MERL-Rose-Hulman/LilyBotCommon/3D Print Parts/NOLONGERUSE/motor_mount/solidworks/Motor Mount.SLDPRT

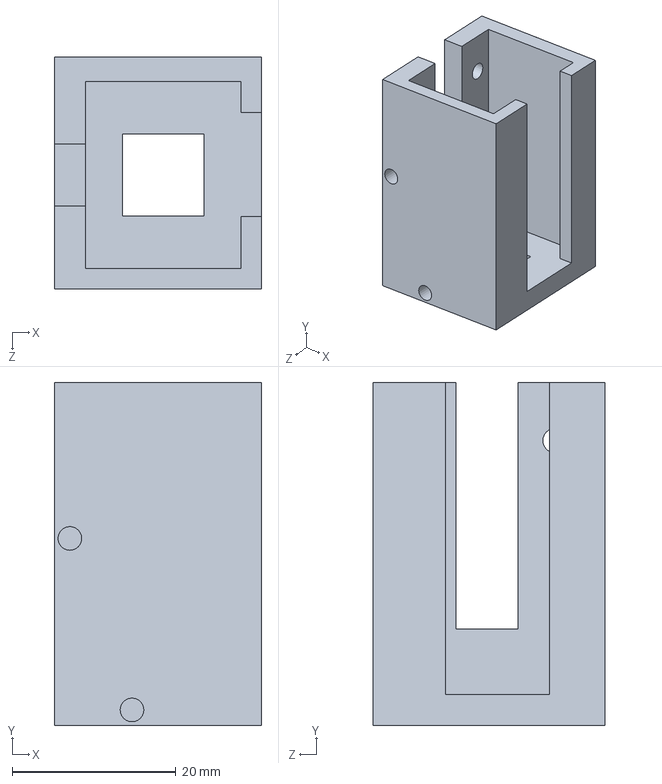
[picture p15: CAD file, 2024-07-10]
3D Print Parts/NOLONGERUSE/motor_mount/solidworks/Motor Mount.SLDPRT
25.4 x 41.9 x 28.4 mm
