MERL-Rose-Hulman/LilyBotCommon/3D Print Parts/NOLONGERUSE/motor_mount/stl/Motor Mount Thick.STL

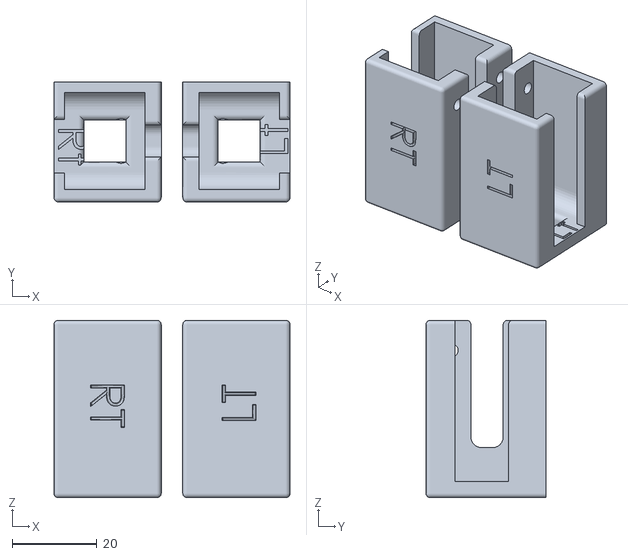
[picture p16: CAD file, 2024-07-10]
3D Print Parts/NOLONGERUSE/motor_mount/stl/Motor Mount Thick.STL
55.8 x 28.4 x 41.9
