MERL-Rose-Hulman/LilyBotCommon/3D Print Parts/sensor_mount/IR/solidworks/IR sensor Attachment _v2.SLDPRT

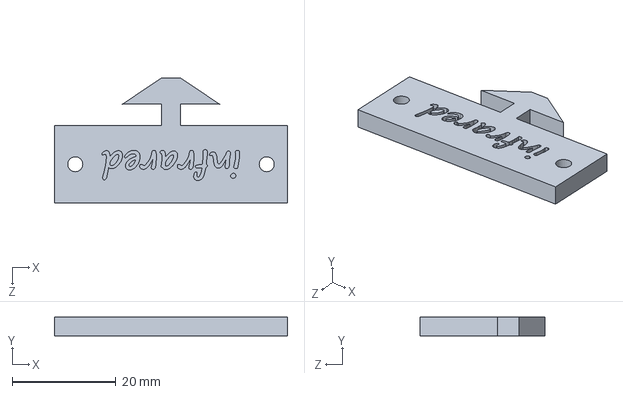
[picture p17: CAD file, 2025-05-02]
3D Print Parts/sensor_mount/IR/solidworks/IR sensor Attachment _v2.SLDPRT
45.0 x 3.58 x 24.2 mm
