MERL-Rose-Hulman/LilyBotCommon/3D Print Parts/sensor_mount/IR/stl/IR Attachment .STL

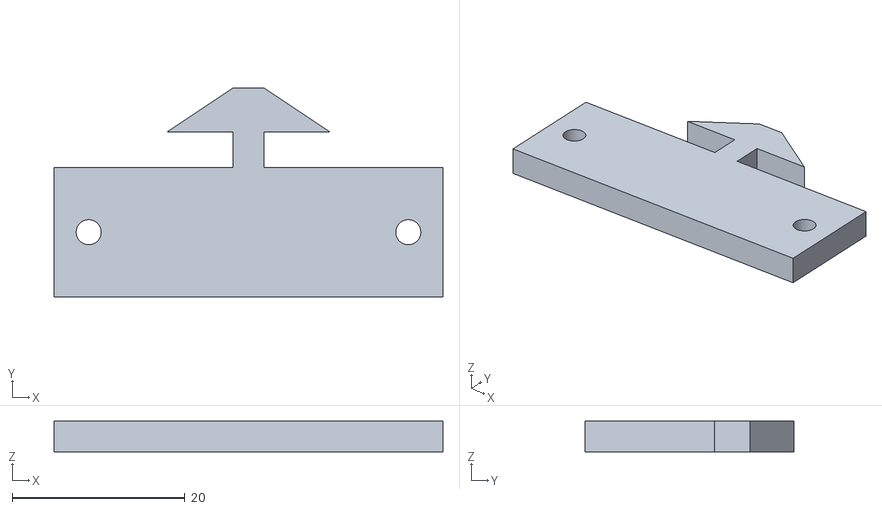
[picture p18: CAD file, 2024-07-10]
3D Print Parts/sensor_mount/IR/stl/IR Attachment .STL
45.0 x 24.2 x 3.58
