MERL-Rose-Hulman/LilyBotCommon/3D Print Parts/sensor_mount/photo/photo sensor Attachment.SLDPRT

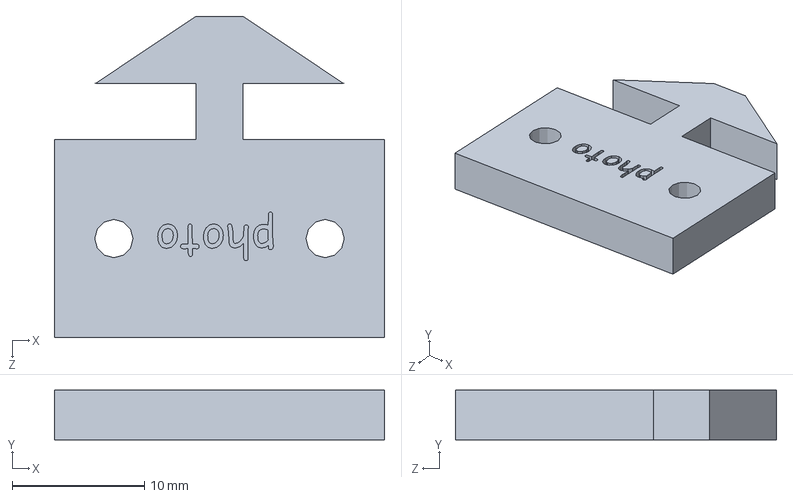
[picture p19: CAD file, 2025-05-02]
3D Print Parts/sensor_mount/photo/photo sensor Attachment.SLDPRT
25.0 x 3.75 x 24.3 mm
