MERL-Rose-Hulman/LilyBotCommon/3D Print Parts/sensor_mount/Sonar/solidworks/Sonar_5V Attachment.SLDPRT

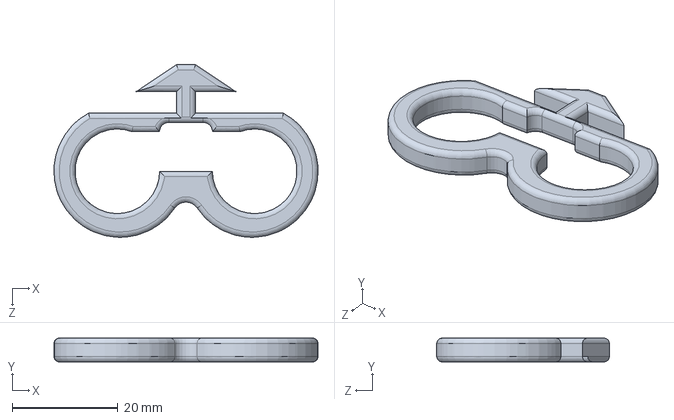
[picture p20: CAD file, 2025-05-09]
3D Print Parts/sensor_mount/Sonar/solidworks/Sonar_5V Attachment.SLDPRT
50.0 x 4.50 x 32.7 mm
