MERL-Rose-Hulman/LilyBotCommon/3D Print Parts/sensor_mount/ToF/solidworks/Tof sensor attachment.SLDPRT

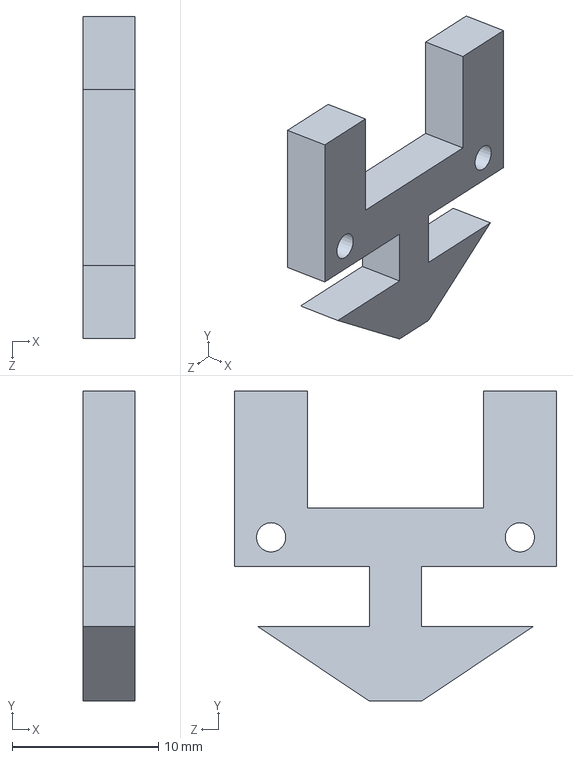
[picture p21: CAD file, 2024-07-10]
3D Print Parts/sensor_mount/ToF/solidworks/Tof sensor attachment.SLDPRT
3.58 x 21.2 x 22.0 mm
