MERL-Rose-Hulman/LilyBotCommon/3D Print Parts/actuator/gripper/stl/finger-left-thin.stl

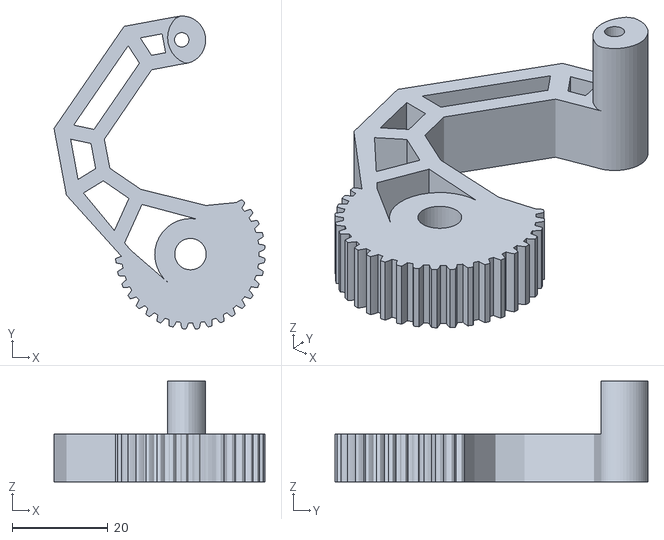
[picture p22: CAD file, 2024-07-10]
3D Print Parts/actuator/gripper/stl/finger-left-thin.stl
44.0 x 65.2 x 21.0
