MERL-Rose-Hulman/LilyBotCommon/3D Print Parts/battery holders/SolidWorks/Microbit Battery Holder.SLDPRT

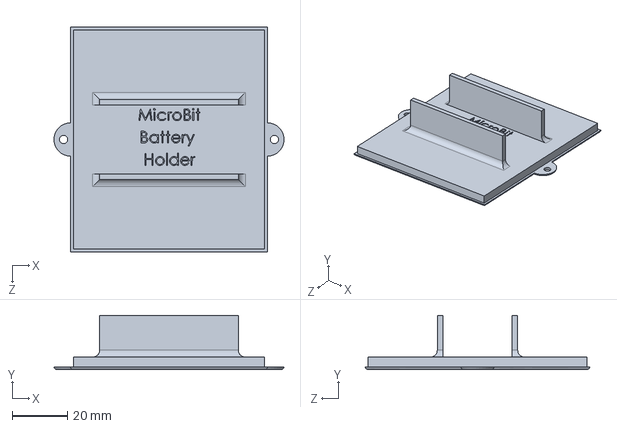
[picture p23: CAD file, 2025-03-31]
3D Print Parts/battery holders/SolidWorks/Microbit Battery Holder.SLDPRT
82.9 x 19.5 x 81.0 mm
