MERL-Rose-Hulman/LilyBotCommon/3D Print Parts/button hole covers/STL/Star Button Hole Cover.stl

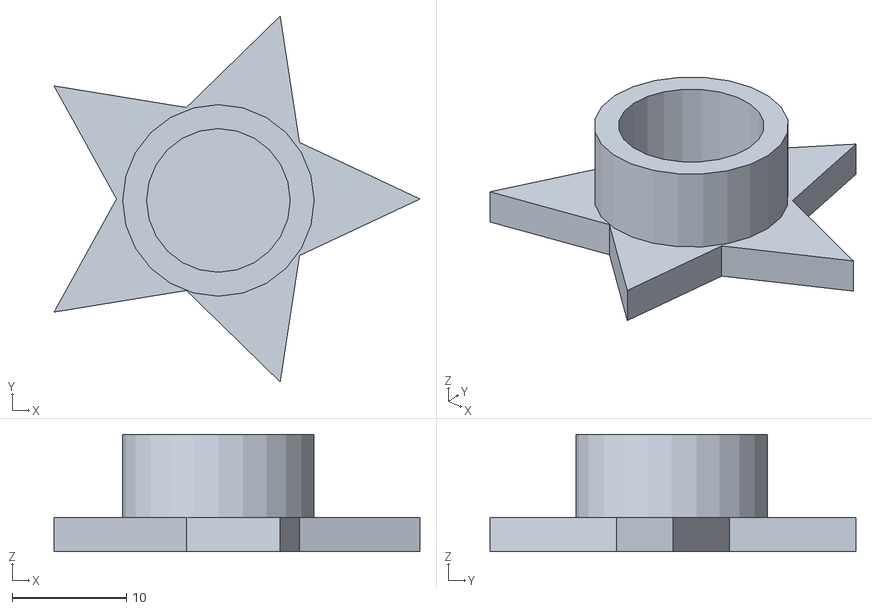
[picture p24: CAD file, 2025-04-04]
3D Print Parts/button hole covers/STL/Star Button Hole Cover.stl
32.0 x 32.0 x 10.2
