MERL-Rose-Hulman/LilyBotCommon/3D Print Parts/cover/NOLONGERUSED/cover tablets/solidworks/Lily Cover Hole Tablet.SLDPRT

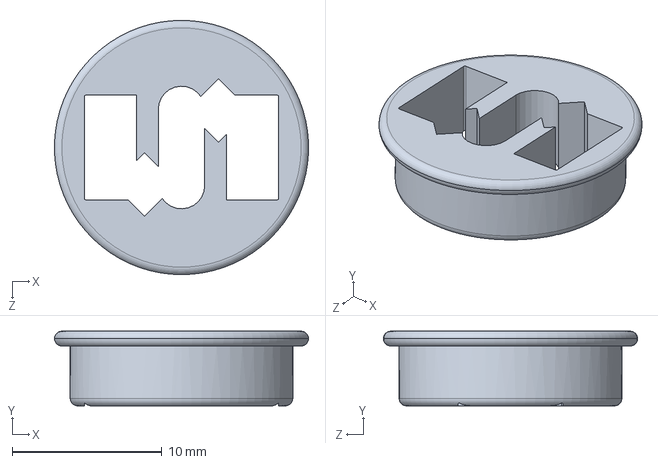
[picture p25: CAD file, 2024-07-10]
3D Print Parts/cover/NOLONGERUSED/cover tablets/solidworks/Lily Cover Hole Tablet.SLDPRT
17.0 x 5.00 x 17.0 mm
