MERL-Rose-Hulman/LilyBotCommon/3D Print Parts/NOLONGERUSE/motor_mount/solidworks/Motor Mount_V2.SLDPRT

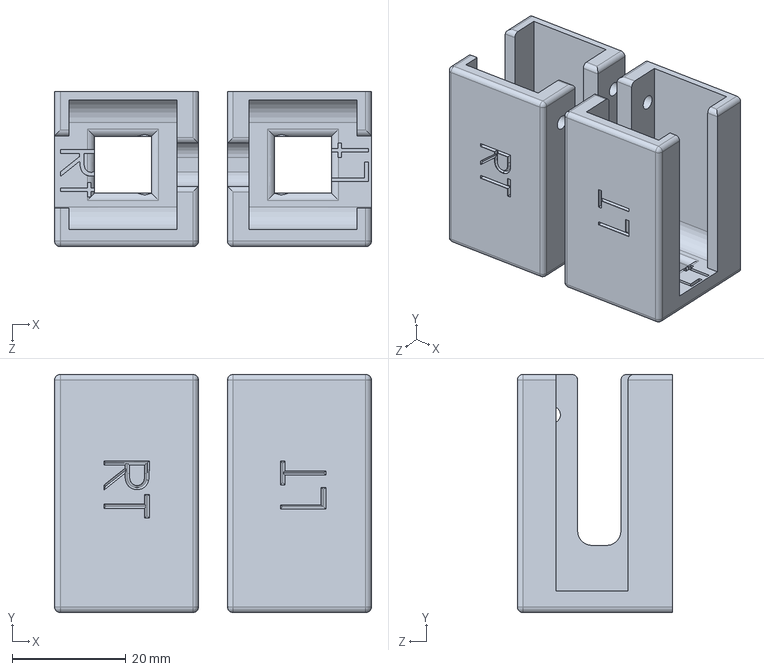
[picture p26: CAD file, 2024-07-10]
3D Print Parts/NOLONGERUSE/motor_mount/solidworks/Motor Mount_V2.SLDPRT
55.8 x 41.9 x 27.4 mm
