MERL-Rose-Hulman/LilyBotCommon/3D Print Parts/sensor_mount/IR/solidworks/IR sensor Attachment .SLDPRT

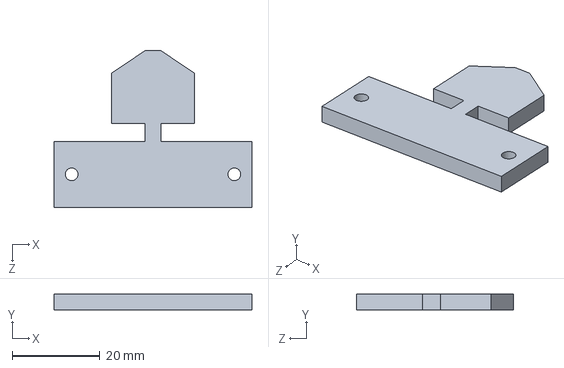
[picture p27: CAD file, 2024-07-10]
3D Print Parts/sensor_mount/IR/solidworks/IR sensor Attachment .SLDPRT
45.0 x 3.58 x 35.6 mm
