MERL-Rose-Hulman/LilyBotCommon/3D Print Parts/sensor_mount/Sonar/solidworks/Sonar_3V Attachment.SLDPRT

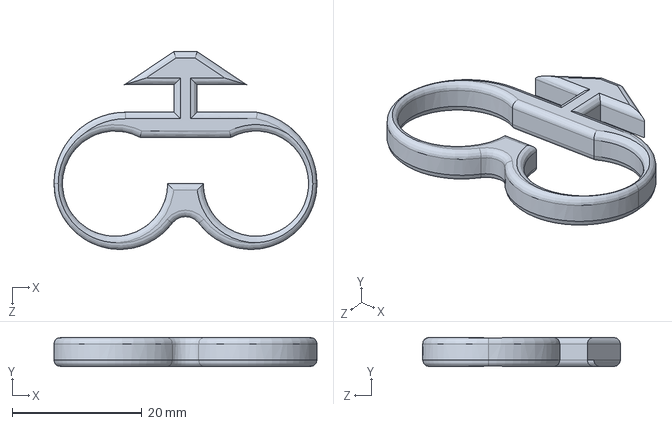
[picture p28: CAD file, 2025-05-09]
3D Print Parts/sensor_mount/Sonar/solidworks/Sonar_3V Attachment.SLDPRT
40.5 x 4.50 x 30.4 mm
