MERL-Rose-Hulman/LilyBotCommon/3D Print Parts/actuator/gripper/stl/finger-pad.stl

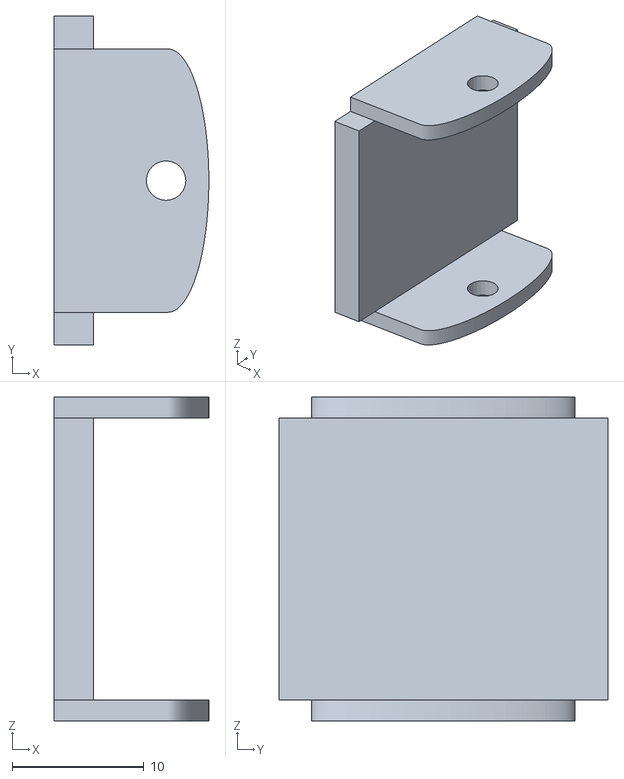
[picture p29: CAD file, 2024-07-10]
3D Print Parts/actuator/gripper/stl/finger-pad.stl
11.8 x 25.0 x 24.6
