MERL-Rose-Hulman/LilyBotCommon/3D Print Parts/button hole covers/STL/Heart Button Hole Cover.stl

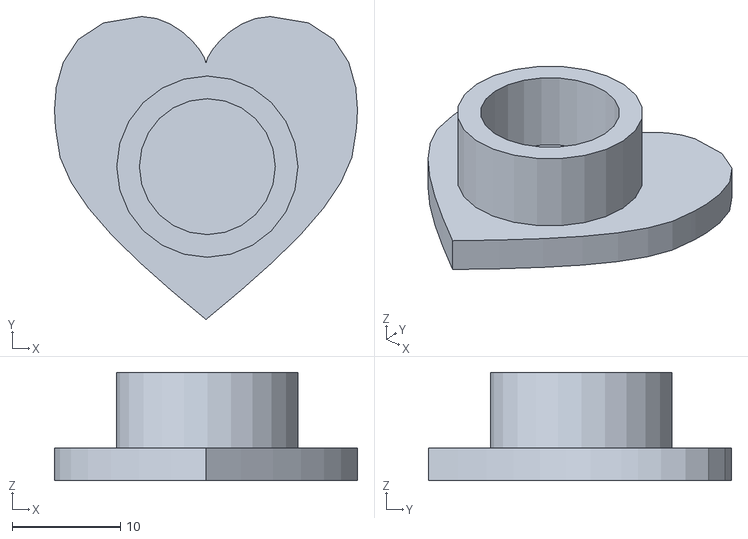
[picture p30: CAD file, 2025-04-04]
3D Print Parts/button hole covers/STL/Heart Button Hole Cover.stl
28.0 x 28.0 x 10.00
