MERL-Rose-Hulman/LilyBotCommon/3D Print Parts/actuator/gripper/stl/top-plate-fixed.stl

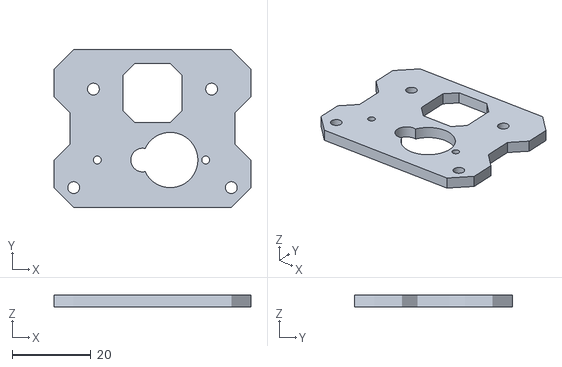
[picture p31: CAD file, 2024-07-10]
3D Print Parts/actuator/gripper/stl/top-plate-fixed.stl
50.0 x 40.0 x 3.00
