MERL-Rose-Hulman/LilyBotCommon/3D Print Parts/sensor_mount/IR/solidworks/IR sensor Attachment Short.SLDPRT

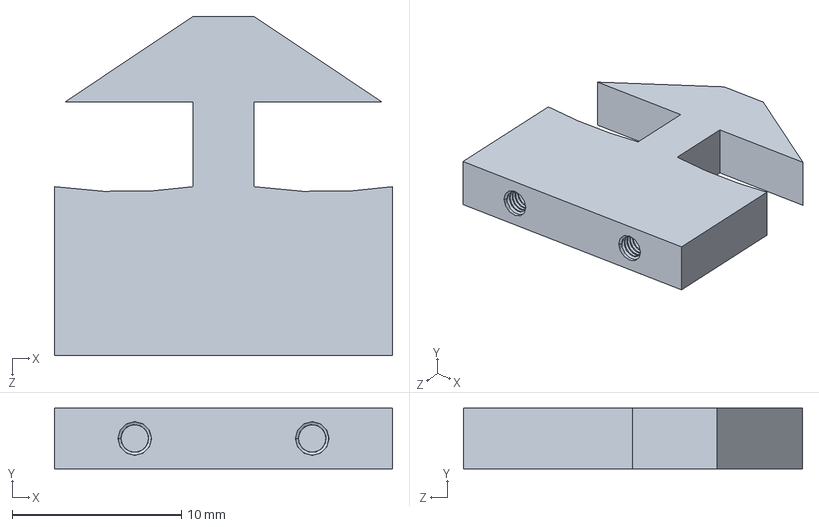
[picture p32: CAD file, 2024-07-10]
3D Print Parts/sensor_mount/IR/solidworks/IR sensor Attachment Short.SLDPRT
20.0 x 3.58 x 20.1 mm
