MERL-Rose-Hulman/LilyBotCommon/3D Print Parts/actuator/gripper/stl/finger-right-thin.stl

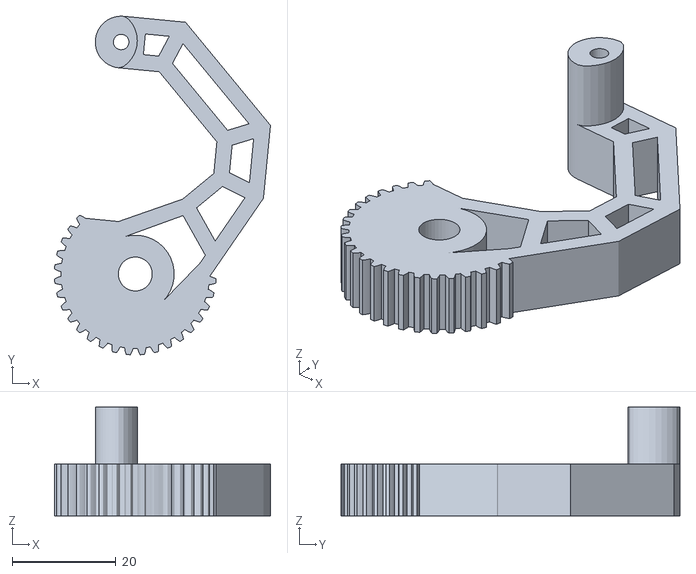
[picture p33: CAD file, 2024-07-10]
3D Print Parts/actuator/gripper/stl/finger-right-thin.stl
41.7 x 65.4 x 21.0
