MERL-Rose-Hulman/LilyBotCommon/3D Print Parts/actuator/gripper/stl/finger-bushing-thin.stl

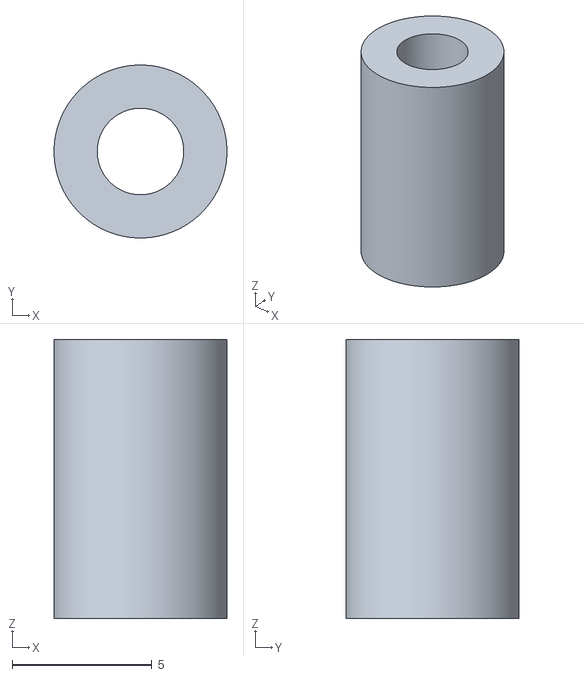
[picture p34: CAD file, 2024-07-10]
3D Print Parts/actuator/gripper/stl/finger-bushing-thin.stl
6.20 x 6.20 x 10.0
