MERL-Rose-Hulman/LilyBotCommon/3D Print Parts/battery holders/SolidWorks/Power Bank Holder.SLDPRT

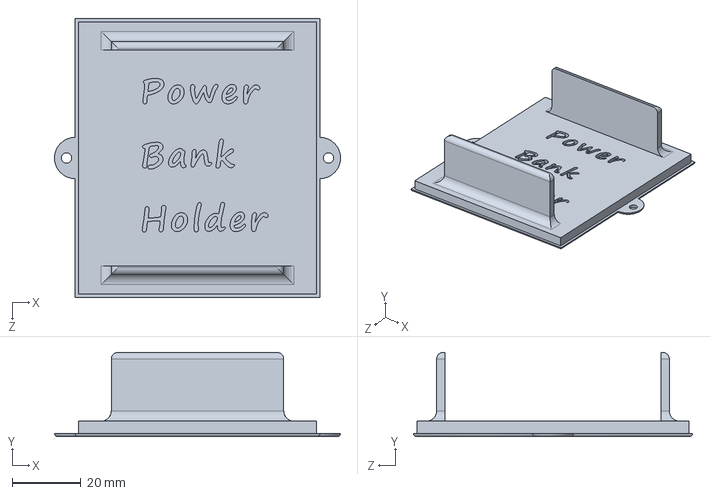
[picture p35: CAD file, 2025-03-31]
3D Print Parts/battery holders/SolidWorks/Power Bank Holder.SLDPRT
82.9 x 24.5 x 81.0 mm
