MERL-Rose-Hulman/LilyBotCommon/3D Print Parts/actuator/gripper/stl/servo-gear.stl

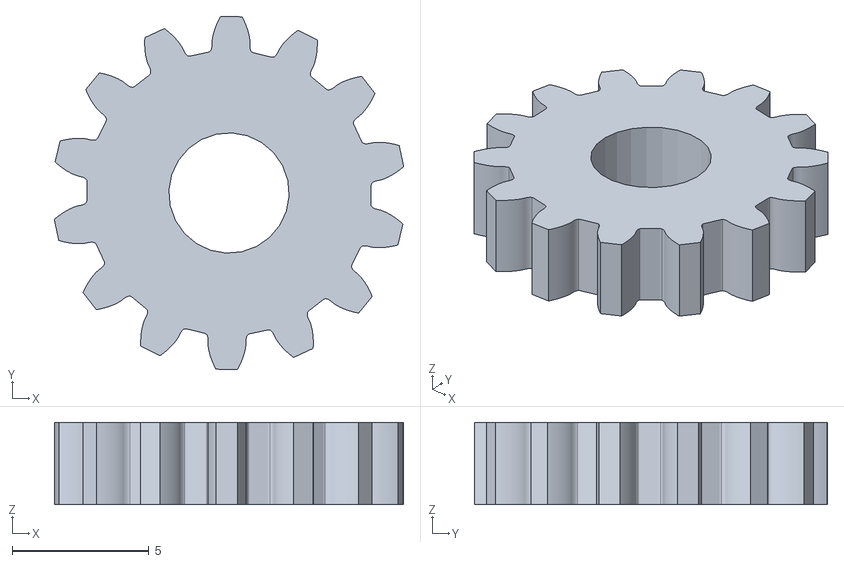
[picture p36: CAD file, 2024-07-10]
3D Print Parts/actuator/gripper/stl/servo-gear.stl
12.8 x 12.9 x 3.00
