MERL-Rose-Hulman/LilyBotCommon/3D Print Parts/actuator/gripper/stl/gripper-base-thin.stl

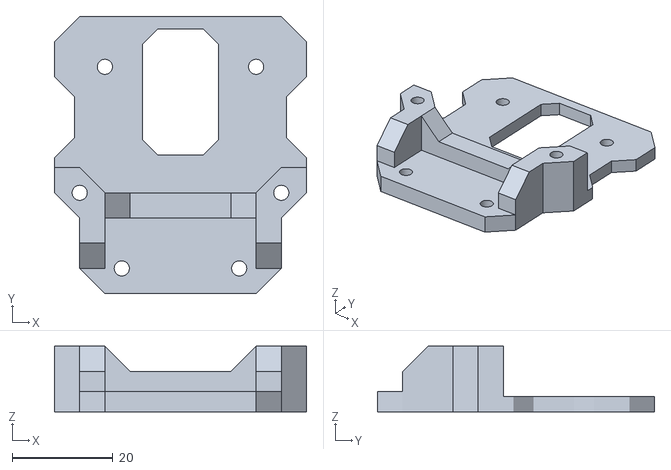
[picture p37: CAD file, 2024-07-10]
3D Print Parts/actuator/gripper/stl/gripper-base-thin.stl
50.0 x 55.0 x 13.0
